Sobreviviente/Fractionated_exhaled_breath/20200309-Volume-differences-among-outputs/results/ebc-c50-total.csv

start | end | volume | start-alveolar | end-alveolar | volume-alveolar | start-dead-space | end-dead-space | volume-dead-space
8.94 | 13.76 | 1.153735427530202 | 9.49 | 14.29 | 0.7267876578773813 | 8.94 | 13.76 | 0.4269477696528208
13.76 | 18.27 | 1.0245032133935454 | 14.29 | 18.92 | 0.6635060401361577 | 13.76 | 18.27 | 0.3609971732573878
18.27 | 23.64 | 1.0750281037965959 | 18.92 | 24.23 | 0.6870290316965323 | 18.27 | 23.64 | 0.3879990721000637
23.64 | 29.21 | 1.0551059362295647 | 24.23 | 29.84 | 0.7061063877140579 | 23.64 | 29.21 | 0.3489995485155068
29.21 | 34.45 | 0.9691989484002657 | 29.84 | 35.11 | 0.6321993801062449 | 29.21 | 34.45 | 0.33699956829402083
34.45 | 39.61 | 0.8819076953949438 | 35.11 | 40.29 | 0.5679082054055556 | 34.45 | 39.61 | 0.31399948998938815
39.61 | 45.06 | 0.9651344783824886 | 40.29 | 45.74 | 0.63313496750012 | 39.61 | 45.06 | 0.33199951088236856
45.06 | 50.31 | 0.8379152210166512 | 45.74 | 50.94 | 0.5409160976201454 | 45.06 | 50.31 | 0.2969991233965058
50.31 | 55.33 | 0.9525442904863872 | 50.94 | 55.99 | 0.6195451129899768 | 50.31 | 55.33 | 0.3329991774964104
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
