Sobreviviente/Fractionated_exhaled_breath/20200309-Volume-differences-among-outputs/results/ebc-meseta-alveolar.csv

start | end | volume
4.39 | 10.05 | 0.7051660786494057
10.05 | 13.98 | 0.3112063000576529
13.98 | 20.06 | 0.52934073893343
20.06 | 25.43 | 0.3639493596984312
25.43 | 30.93 | 0.27140496556494564
30.93 | 36.58 | 0.2753361864457975
36.58 | 42.48 | 0.19228600097719015
42.48 | 48.92 | 0.4852257883829198
48.92 | 54.76 | 0.3794235308896257
54.76 | 60.75 | 0.2509267545306871
60.75 | 66.03 | 0.1913361829872876
66.03 | 71.48 | 0.2069328607091895
71.48 | 77.84 | 0.31183194951625987
77.84 | 83.5 | 0.41326628213999733
83.5 | 89.21 | 0.33072189479363695
89.21 | 95.14 | 0.28500439907411607
95.14 | 101.67 | 0.3790496166895493
101.67 | 107.46 | 0.42384346525790656
107.46 | 113.6 | 0.4331806695390518
113.6 | 118.92 | 0.18999724905564883
118.92 | 124.46 | 0.19733619425391538
124.46 | 130.44 | 0.38866304187991463
130.44 | 136.09 | 0.3716943657935071
136.09 | 141.8 | 0.1852930006120583
141.8 | 147.93 | 0.4690488645269366
147.93 | 154.05 | 0.415505158329325
154.05 | 160.42 | 0.4241775721726922
160.42 | 165.84 | 0.22405646715809313
165.84 | 171.28 | 0.21885568079943923
171.28 | 177.0 | 0.2429748895235442
177.0 | 182.69 | 0.24699932656057388
182.69 | 188.21 | 0.2448886884462064
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
