Sobreviviente/Fractionated_exhaled_breath/20200309-Volume-differences-among-outputs/results/ebc-meseta-dead-space.csv

start | end | volume
1.62 | 8.13 | 1.0349996137380901
8.13 | 13.0 | 0.7949996199032723
13.0 | 18.82 | 0.8402031314732648
18.82 | 24.25 | 0.8119994673044343
24.25 | 29.87 | 0.4949993722544896
29.87 | 35.57 | 0.6389996139506601
35.57 | 41.4 | 0.5689996075935525
41.4 | 47.98 | 0.6669994431213506
47.98 | 53.71 | 0.6699996195422435
53.71 | 59.7 | 0.6999989893576164
59.7 | 65.01 | 0.6659995550535653
65.01 | 70.53 | 0.7099996015764792
70.53 | 76.84 | 0.6469990471385063
76.84 | 82.59 | 0.6539996000234978
82.59 | 88.32 | 0.6189995832589724
88.32 | 94.22 | 0.6819995474011248
94.22 | 100.7 | 0.6529992022507938
100.7 | 106.57 | 0.6769995759730492
106.57 | 112.29 | 0.6939996096837566
112.29 | 117.95 | 0.8527492384149008
117.95 | 123.44 | 0.600999451855985
123.44 | 129.43 | 0.6879973015258247
129.43 | 134.92 | 0.6319995314723704
134.92 | 140.86 | 0.660998840685772
140.86 | 146.96 | 0.6119996150016147
146.96 | 153.1 | 0.6939996087951422
153.1 | 159.41 | 0.6219990738646027
159.41 | 164.88 | 0.6859996179254365
164.88 | 170.34 | 0.6839988508062176
170.34 | 175.95 | 0.6120350663995253
175.95 | 181.02 | 0.6859989505156454
181.02 | 187.18 | 0.6539996080801366
187.18 | 193.29 | 0.5229988079692867
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
