Sobreviviente/Fractionated_exhaled_breath/20200309-Volume-differences-among-outputs/results/ebc-meseta-total.csv

start | end | volume | start-alveolar | end-alveolar | volume-alveolar | start-dead-space | end-dead-space | volume-dead-space
1.62 | 8.13 | 1.740165692387496 | 4.39 | 10.05 | 0.7051660786494057 | 1.62 | 8.13 | 1.0349996137380901
8.13 | 13.0 | 1.106205919960925 | 10.05 | 13.98 | 0.3112063000576529 | 8.13 | 13.0 | 0.7949996199032723
13.0 | 18.82 | 1.369543870406695 | 13.98 | 20.06 | 0.52934073893343 | 13.0 | 18.82 | 0.8402031314732648
18.82 | 24.25 | 1.1759488270028655 | 20.06 | 25.43 | 0.3639493596984312 | 18.82 | 24.25 | 0.8119994673044343
24.25 | 29.87 | 0.7664043378194352 | 25.43 | 30.93 | 0.27140496556494564 | 24.25 | 29.87 | 0.4949993722544896
29.87 | 35.57 | 0.9143358003964576 | 30.93 | 36.58 | 0.2753361864457975 | 29.87 | 35.57 | 0.6389996139506601
35.57 | 41.4 | 0.7612856085707427 | 36.58 | 42.48 | 0.19228600097719015 | 35.57 | 41.4 | 0.5689996075935525
41.4 | 47.98 | 1.1522252315042705 | 42.48 | 48.92 | 0.4852257883829198 | 41.4 | 47.98 | 0.6669994431213506
47.98 | 53.71 | 1.0494231504318692 | 48.92 | 54.76 | 0.3794235308896257 | 47.98 | 53.71 | 0.6699996195422435
53.71 | 59.7 | 0.9509257438883034 | 54.76 | 60.75 | 0.2509267545306871 | 53.71 | 59.7 | 0.6999989893576164
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
