Sobreviviente/Fractionated_exhaled_breath/20200309-Volume-differences-among-outputs/results/c50-volumes.png

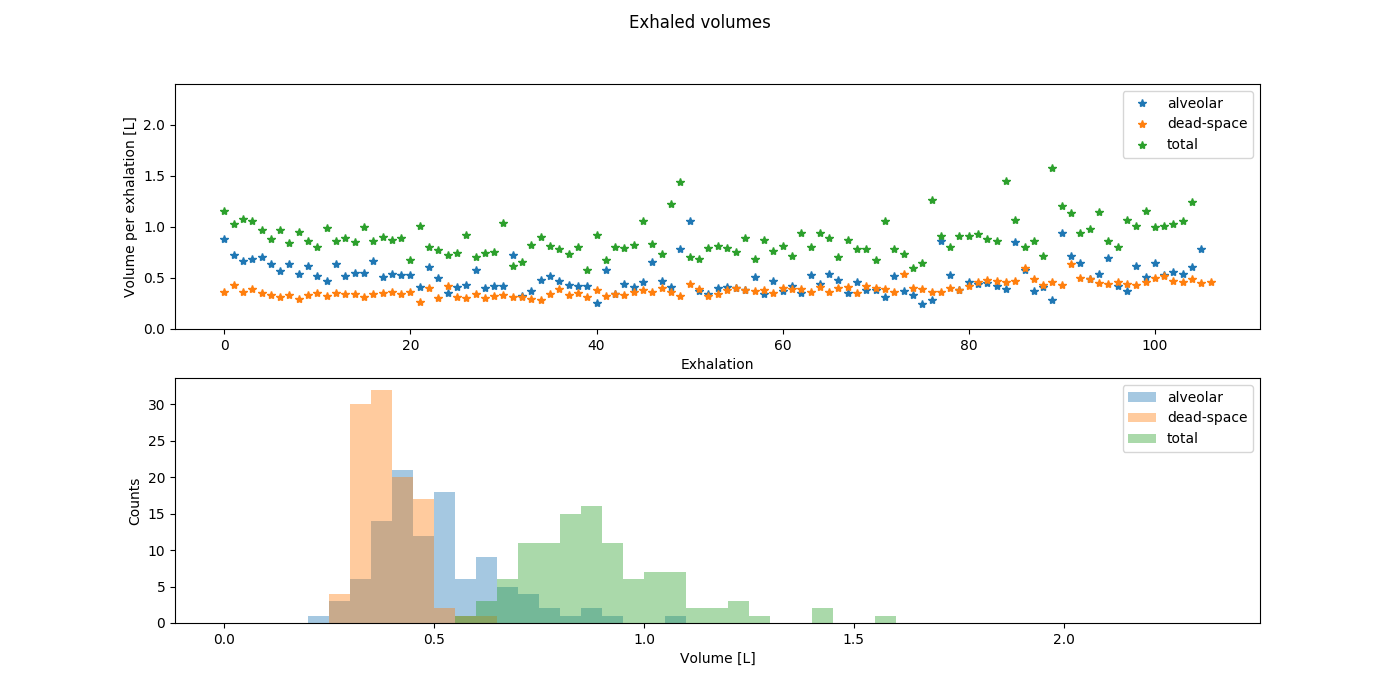
20200309-Volume-differences-among-outputs/results/c50-volumes.png
