Sobreviviente/Fractionated_exhaled_breath/20200309-Volume-differences-among-outputs/results/meseta-flow.png

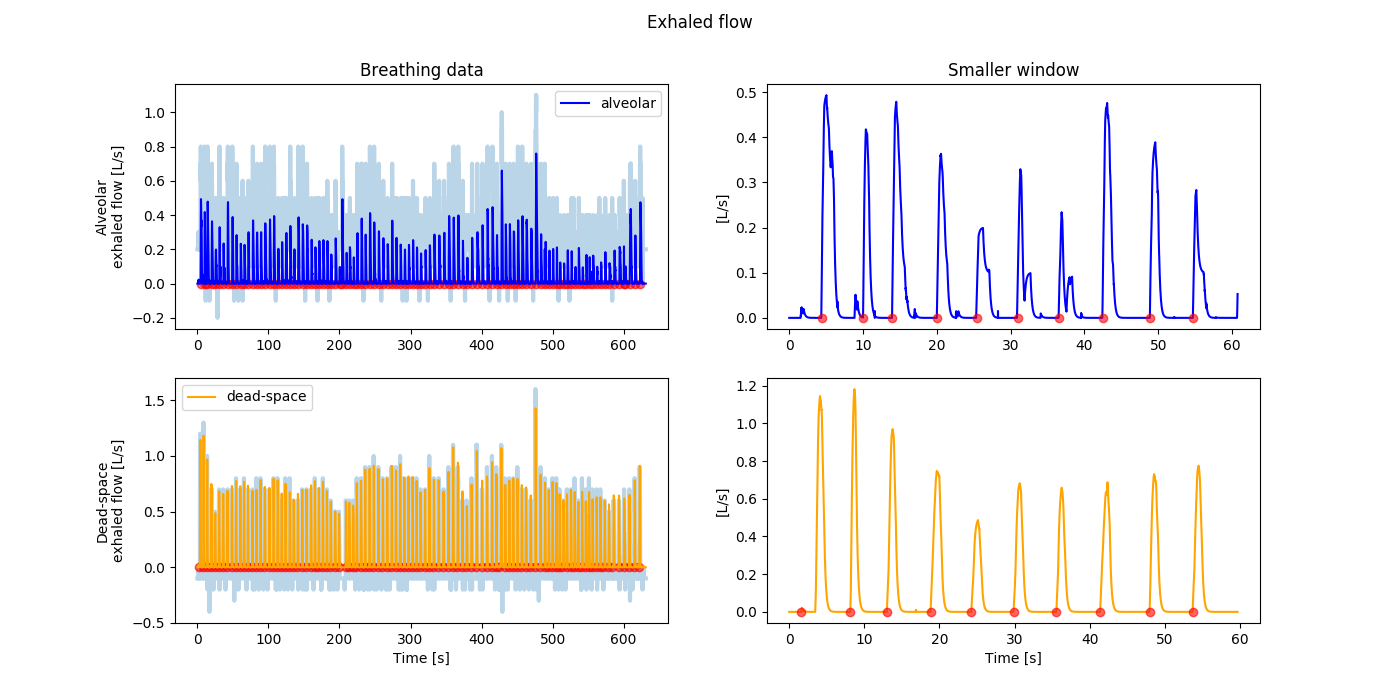
20200309-Volume-differences-among-outputs/results/meseta-flow.png
