Sobreviviente/Fractionated_exhaled_breath/20200309-Volume-differences-among-outputs/results/meseta-volumes.png

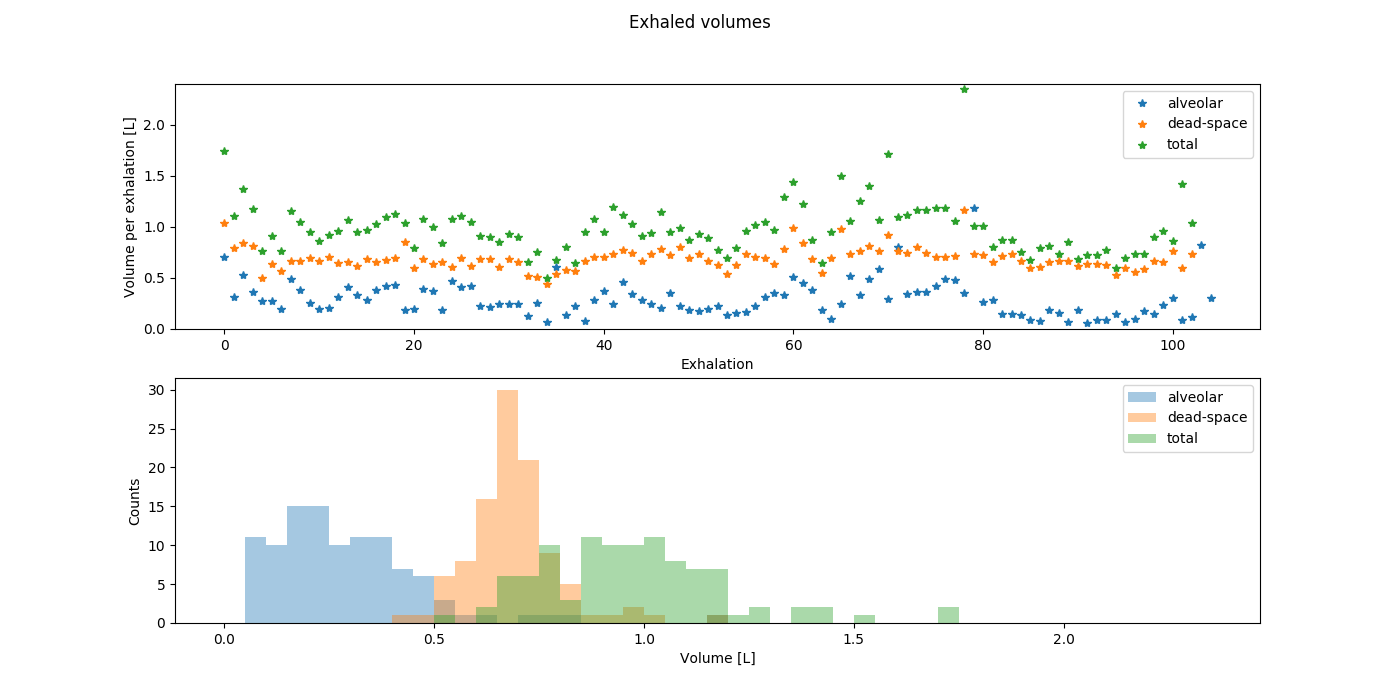
20200309-Volume-differences-among-outputs/results/meseta-volumes.png
