Sobreviviente/Fractionated_exhaled_breath/fractionated_exhaled_breath_final/fractionated_exhaled_breath_final/defines.h

#ifndef DEFINES_H
#define DEFINES_H

// ********** Parametros ********
#define SUMA_TIEMPO 0 // 150000 // [us]

// ********** Pinouts ********
#define ledPin 13
#define Bomba1 11
#define Bomba2 12
#define Presion 20
#define co2_1 23
#define co2_2 22
#define valv_blanca_1 16 //1 es el de la derecha
#define valv_negra_2 17  // 2 es el de la izquierda 
#define valv_blanca_2 18
#define valv_negra_1 19 
#define pin_switch 8

// ********** Algoritmos ********
#define PCe  0
#define Ce50 1

// ********** Umbrales Presión ********

#define umbral_high 3.1
#define umbral_low 3.0

#endif // DEFINES_H
